TheStaticTurtle/Open433/homeassistant_open433/rcswitch.py

import base64
import threading
import time
from threading import Thread

import serial
import logging
import struct

root_logger = logging.getLogger(__name__)


def zero_cut(raw):
	if type(raw) != str:
		raw = raw.decode("utf-8")
	try:
		return raw[:raw.index('\x00')]
	except ValueError:
		return raw


def getPacketType(raw):
	if raw == "timeout":
		return raw
	fmt = "16s"
	size = struct.calcsize(fmt)
	data = struct.unpack(fmt, raw[:size])
	return zero_cut(data[0].decode("utf-8"))


class packets(object):
	def __init__(self):
		super(packets, self).__init__()
		self.ReceiveTypes = [self.ReceivedSignal, self.ReceivedAck]
		self.SendTypes = [self.SendDecimal, self.SendConfig]

	class ReceivedSignal(object):
		"""docstring for received_signal_packet_t"""

		def __init__(self, logger):
			super(packets.ReceivedSignal, self).__init__()
			self.format = "<17sIIHHH"

			self.time = -1
			self.decimal = -1
			self.length = -1
			self.delay = -1
			# self.raw     = None
			self.protocol = 0
			self.logger = logger

		def __str__(self):
			return "<ReceivedSignal time=" + str(self.time) + " decimal=" + str(
				self.decimal) + " length=" + str(
				self.length) + " delay=" + str(self.delay) + " protocol=" + str(self.protocol) + ">"

		def parse(self, raw):
			try:
				unpacked = struct.unpack(self.format, bytearray(raw))
				self.time = unpacked[1]
				self.decimal = unpacked[2]
				self.length = unpacked[3]
				self.delay = unpacked[4]
				self.protocol = unpacked[5]
				return self
			except struct.error:
				if self.logger is not None:
					self.logger.error("[ReceivedSignal] Error decode packet: " + base64.b64encode(raw) + " ")
					return self

	class ReceivedAck(object):
		"""docstring for received_signal_packet_t"""

		def __init__(self, logger):
			super(packets.ReceivedAck, self).__init__()
			self.format = "<17sI32s"

			self.time = -1
			self.msg = ""
			self.logger = logger

		def __str__(self):
			return "<ReceivedSignal time=" + str(self.time) + " msg=\"" + self.msg + "\">"

		def parse(self, raw):
			try:
				unpacked = struct.unpack(self.format, bytearray(raw))
				self.time = unpacked[1]
				self.msg = unpacked[2].decode("utf-8")
				return self
			except struct.error:
				if self.logger is not None:
					self.logger.error("[ReceivedAck] Error decode packet: " + base64.b64encode(raw) + " ")
					return self

	class SendDecimal(object):
		"""This packet is used to send a decimal code over the air"""

		def __init__(self, value, length, delay, protocol):
			super(packets.SendDecimal, self).__init__()
			self.format = "<16sIHHH"

			self.value = value
			self.length = length
			self.delay = delay
			self.protocol = protocol

		def __str__(self):
			return "<SendDecimal value=" + str(self.value) + " length=" + str(self.length) + " delay=" + str(
				self.delay) + " protocol=" + str(self.protocol) + "> "

		def pack(self):
			packed = struct.pack(
				self.format,
				b"send_decimal",
				self.value,
				self.length,
				self.delay,
				self.protocol
			)
			return packed

	class SendConfig(object):
		"""This packet is used to send a decimal code over the air"""

		def __init__(self, signal_reapeat, receive_tolerance=60):
			super(packets.SendConfig, self).__init__()
			self.format = "<16sHH"

			self.signal_reapeat = signal_reapeat
			self.receive_tolerance = receive_tolerance

		def __str__(self):
			return "<SendConfig signal_reapeat=" + str(self.signal_reapeat) + " receive_tolerance=" + str(
				self.receive_tolerance) + "> "

		def pack(self):
			packed = struct.pack(
				self.format,
				b"rcswitch_conf",
				self.signal_reapeat,
				self.receive_tolerance,
			)
			return packed


class RCSwitch(object):
	"""docstring for RCSwitch"""

	def __init__(self, port, speed=9600, logger=root_logger):
		super(RCSwitch, self).__init__()
		self._gotAck = False
		self.logger = logger
		self.signal_repeat = 3
		self.receive_tolerance = 60
		self.com_port = port
		self.com_speed = speed
		self._shouldWaitForAck = False
		self._timeout = 0.1
		self._incomingPacketListeners = []
		self._bufferedPackets = []
		self._error_listeners = []
		self._polling_thread = None
		self.serial = serial.Serial(self.com_port, self.com_speed, timeout=0.1, xonxoff=False, rtscts=False)

	def serial_sync(self, sync_word, timeout: float = 20, should_print_timeout_error=True):
		try:
			tstart = time.time()
			buf = bytes()
			while buf[-len(sync_word):] != bytes(sync_word.encode("ascii")):
				buf += bytes(self.serial.read())
				if timeout != -1 and (tstart + timeout < time.time()):
					if should_print_timeout_error:
						self.logger.error("Timeout while reading start sync")
					return "timeout"
			self.serial.read(2)
		except serial.serialutil.SerialException as e:
			for listener in self._error_listeners:
				listener(e)
			raise e

	def serial_sync_end(self, sync_word, timeout: float = -1, should_print_timeout_error=True):
		try:
			time_start = time.time()
			buf = bytes()
			while buf[-len(sync_word):] != bytes(sync_word.encode("ascii")):
				buf += bytes(self.serial.read())
				if timeout != -1 and (time_start + timeout < time.time()):
					if should_print_timeout_error:
						self.logger.error("Timeout while reading end sync")
					return "timeout"
			return buf[:-len(sync_word)]
		except serial.serialutil.SerialException as e:
			for listener in self._error_listeners:
				listener(e)
			raise e

	def receive_packet(self, timeout: float = -1):
		try:
			time_start = time.time()
			while (timeout == -1) or (time_start + timeout > time.time()):
				self.serial_sync("START", should_print_timeout_error=False)
				raw = self.serial_sync_end("END", timeout=timeout, should_print_timeout_error=False)
				packet_type = getPacketType(raw)
				if packet_type == "receive_signal":
					p = packets.ReceivedSignal(self.logger).parse(raw)
					self.logger.info("Received packet: " + str(p))
					return p
				if packet_type == "ack":
					self.logger.info("Received ACK message")
					return packets.ReceivedAck(self.logger).parse(raw)
			return None
		except Exception as e:
			for listener in self._error_listeners:
				listener(e)
			raise e

	def listen(self, timeout=-1):
		return self._listen(self, timeout=timeout)

	class _listen:
		def __init__(self, parent, timeout=-1):
			self.parent = parent
			self.timeout = timeout
			self.closed = False

		def __iter__(self):
			return self

		def next(self):
			return self.__next__()

		def __next__(self):
			time_start = time.time()
			while True:
				if self.closed or (self.timeout != -1 and (time_start + self.timeout < time.time())):
					raise StopIteration

				data = self.parent.receive_packet(timeout=0.75 if self.timeout == -1 else self.timeout)
				if data is not None:
					return data

	def libWaitForAck(self, should_wait, timeout=0.1):
		self._shouldWaitForAck = should_wait
		self._timeout = timeout

	def setRepeatTransmit(self, repeat):
		if self.signal_repeat == repeat:
			# No need it's the same
			return True
		self.signal_repeat = max(repeat, 1)
		return self.send(packets.SendConfig(self.signal_repeat, self.receive_tolerance))

	def setReceiveTolerance(self, tol):
		if self.receive_tolerance == tol:
			# No need it's the same
			return True
		self.receive_tolerance = min(max(tol, 0), 100)
		return self.send(packets.SendConfig(self.signal_repeat, self.receive_tolerance))

	def send(self, packet):
		try:
			if type(packet) in packets().SendTypes:
				self.serial.write(b"START\r\n")
				self.serial.write(packet.pack())
				self.serial.write(b"END\r\n")
				self.logger.info("Sending packet: " + str(packet))
				if self._shouldWaitForAck:
					return self._waitForAck(timeout=self._timeout)
				else:
					return True
			else:
				self.logger.error("Passed packet can't be sent " + str(type(packet)))
				raise ValueError("Passed packet can't be sent " + str(type(packet)))
		except Exception as e:
			for listener in self._error_listeners:
				listener(e)
			raise e

	def _waitForAck(self, timeout=-1.0):
		tstart = time.time()
		while not self._gotAck:
			time.sleep(.05)
			if timeout != -1 and (tstart + timeout < time.time()):
				self.logger.warning("Timedout while reading ack")
				return False
		self._gotAck = False
		return True

	def _packetReceiver(self):
		iterator = self._listen(self, timeout=-1)
		for packet in iterator:
			if isinstance(packet, packets.ReceivedAck):
				self._gotAck = True
			elif packet is not None:
				self._bufferedPackets.append(packet)
				self._dispatchPacketsToListeners()
			else:
				continue

	def startReceivingThread(self):
		if self._polling_thread is None:
			self._polling_thread = Thread(target=self._packetReceiver)
			self._polling_thread.start()

	def _dispatchPacketsToListeners(self):
		if len(self._incomingPacketListeners) > 0:
			while len(self._bufferedPackets) > 0:
				packet = self._bufferedPackets.pop()
				for listener in self._incomingPacketListeners:
					listener(packet)

	def addIncomingPacketListener(self, who):
		self._incomingPacketListeners.append(who)

	def removeIncomingPacketListener(self, who):
		if who in self._incomingPacketListeners:
			self._incomingPacketListeners.remove(who)

	def addErrorListener(self, who):
		self._error_listeners.append(who)

	def removeErrorListener(self, who):
		if who in self._incomingPacketListeners:
			self._incomingPacketListeners.remove(who)

	def cleanup(self):
		self.serial.close()
		if self._polling_thread is not None:
			self._polling_thread.join()

	def prepare(self):
		pass
